Statkus/motion_platform/hardware/seat_mover/sway_motor_mount_top.FCStd

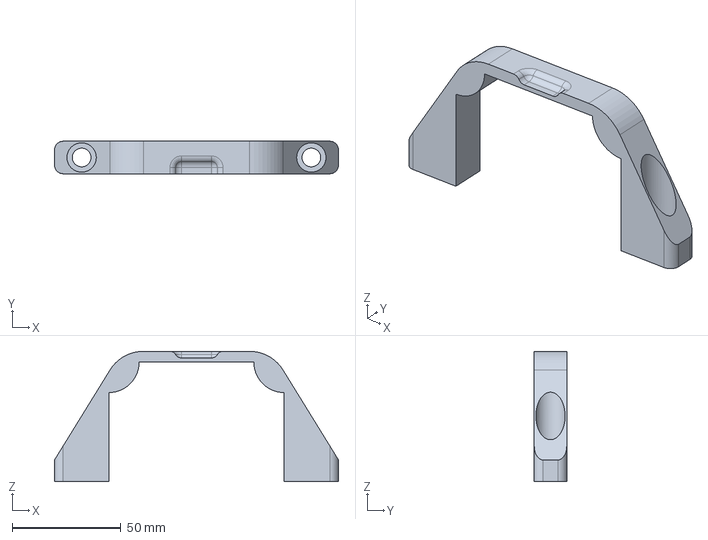
[picture p13: CAD file, 2025-09-17]
hardware/seat_mover/sway_motor_mount_top.FCStd
130.8 x 15.0 x 60.0 mm
