Statkus/motion_platform/hardware/parts_library/zip_tie_2x1_mm_to_2020_profile.FCStd

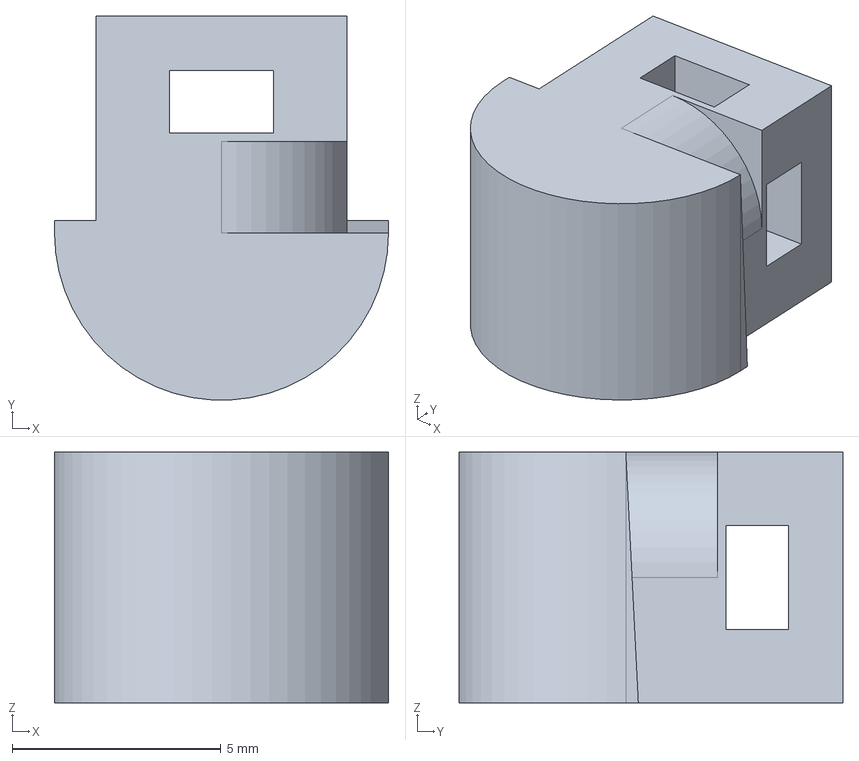
[picture p14: CAD file, 2025-10-09]
hardware/parts_library/zip_tie_2x1_mm_to_2020_profile.FCStd
8.00 x 9.19 x 6.00 mm
