Statkus/motion_platform/hardware/seat_mover/seat.FCStd

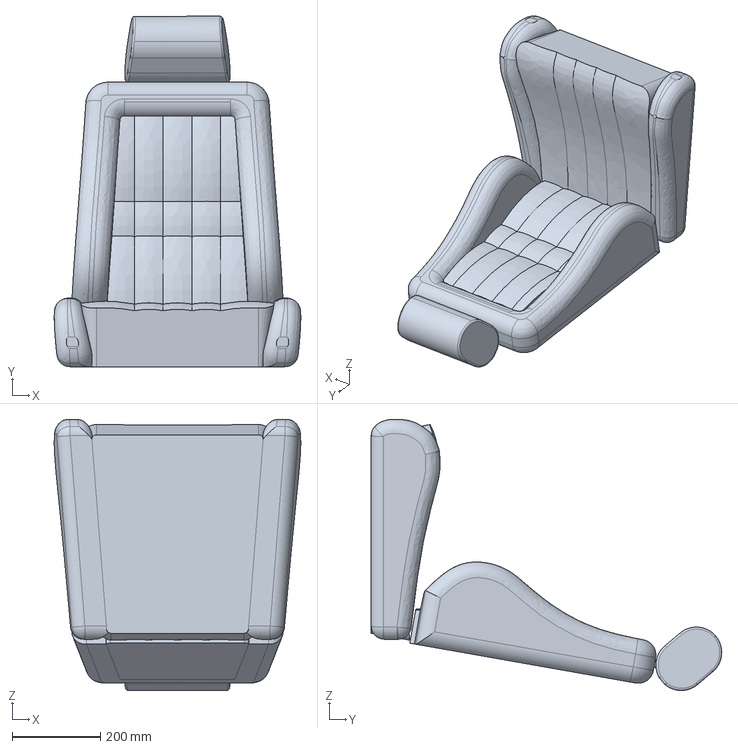
[picture p15: CAD file, 2025-09-17]
hardware/seat_mover/seat.FCStd
559.4 x 795.1 x 614.7 mm
