Statkus/motion_platform/hardware/parts_library/SHF25.FCStd

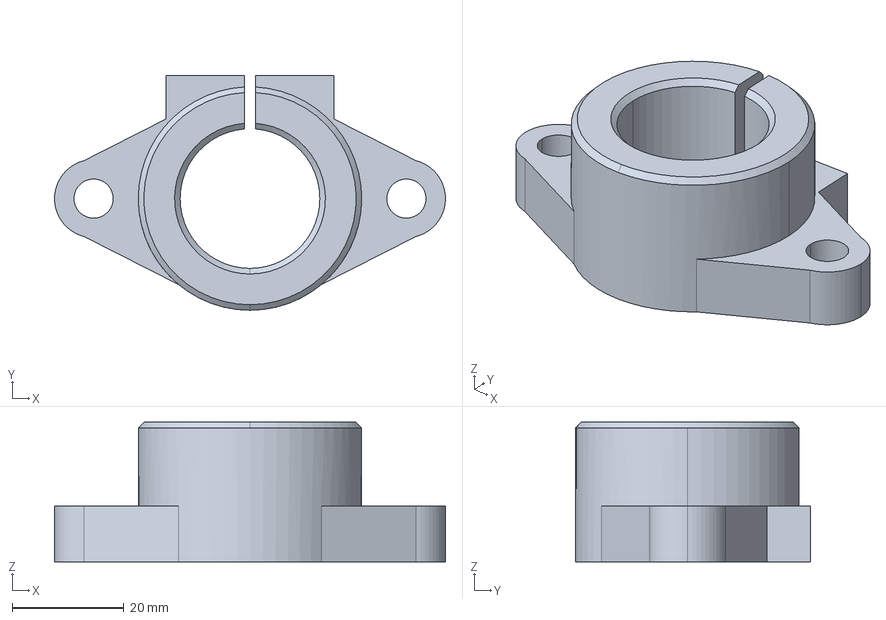
[picture p16: CAD file, 2025-08-28]
hardware/parts_library/SHF25.FCStd
70.0 x 42.0 x 25.0 mm
