Statkus/motion_platform/hardware/seat_mover/sway_motor_mount_bottom.FCStd

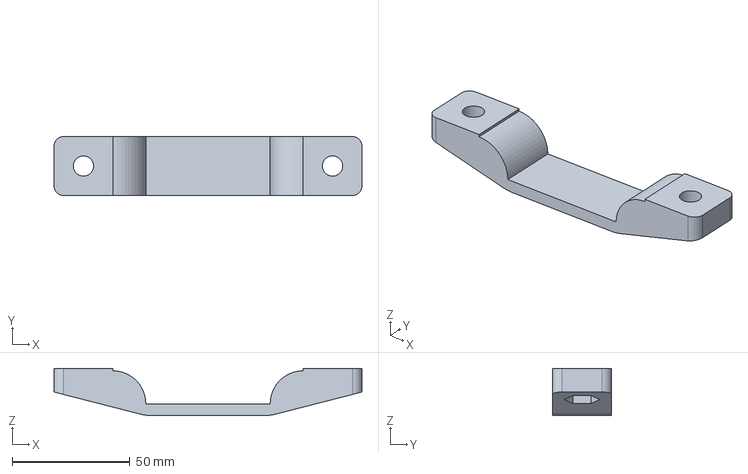
[picture p17: CAD file, 2025-09-17]
hardware/seat_mover/sway_motor_mount_bottom.FCStd
130.8 x 25.0 x 20.0 mm
