Statkus/motion_platform/hardware/parts_library/DSG16H_to_SH25.FCStd

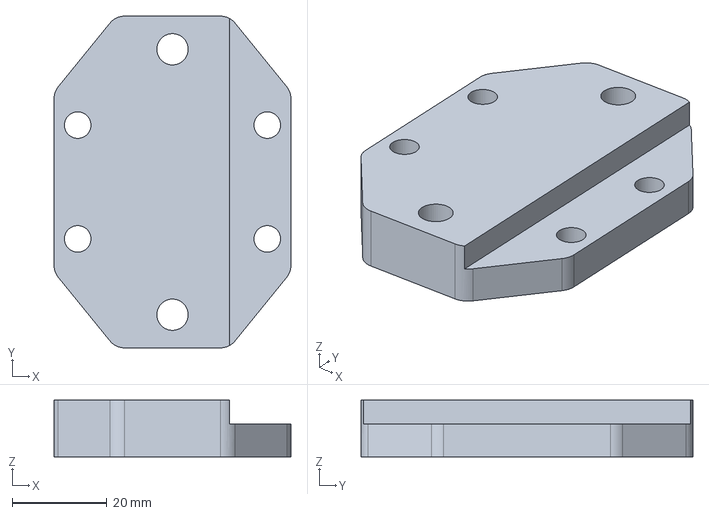
[picture p18: CAD file, 2025-08-28]
hardware/parts_library/DSG16H_to_SH25.FCStd
50.0 x 70.0 x 12.0 mm
