Statkus/motion_platform/hardware/parts_library/SFU1605.FCStd

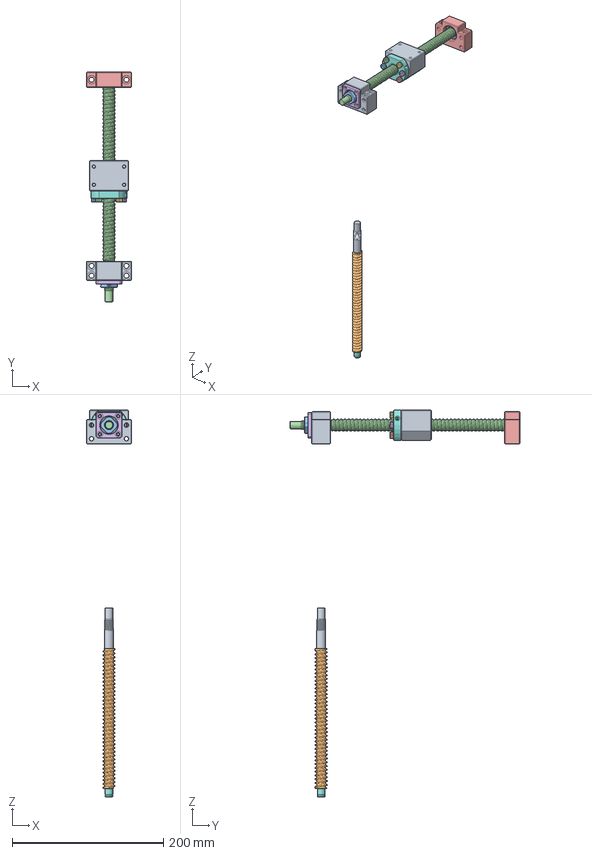
[picture p19: CAD file, 2025-08-28]
hardware/parts_library/SFU1605.FCStd
60.0 x 303.5 x 511.5 mm
BK12 v3
BK12 v004
BK12 v005
BK12 v006
BK12 v007
BK12 v008
BK12 v009
BK12 v010
BK12 v011
BK12 v012
BK12 v013
BK12 v014
BK12 v015
BK12 v016
BK12 v017
BK12 v018
BK12 v019
BK12 v020
BK12 v021
BK12 v022
BK12 v023
BK12 v024
BK12 v025
BK12 v026
BK12 v027
BK12 v028
BK12 v029
BK12 v030
BK12 v031
BK12 v032
BK12 v033
BK12 v034
BK12 v035
BK12 v036
BK12 v037
SFU1605_ball_screw_300mm
BF12 v4
BF12 v005
BF12 v006
BF12 v007
BF12 v008
BF12 v009
BF12 v010
BF12 v011
BF12 v012
BF12 v013
BF12 v014
SFU1605_ball_screw_nut
DSG16H
screw_DIN912_M5x20_000
screw_DIN912_M5x20_001
screw_DIN912_M5x20_002
screw_DIN912_M5x20_003
screw_DIN912_M5x20_004
screw_DIN912_M5x20_005
