Statkus/motion_platform/hardware/seat_mover/sway_motor_mount_side.FCStd

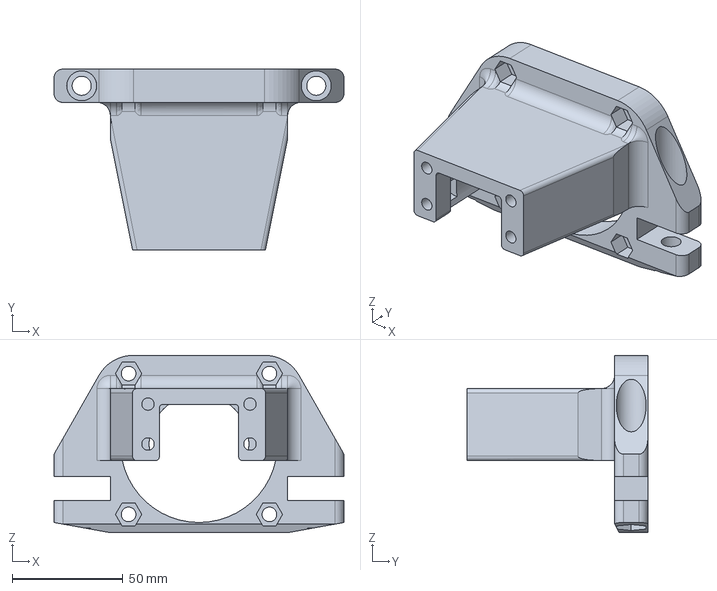
[picture p20: CAD file, 2025-09-17]
hardware/seat_mover/sway_motor_mount_side.FCStd
130.8 x 81.5 x 80.0 mm
