Statkus/motion_platform/hardware/parts_library/SC25UU_to_SH25.FCStd

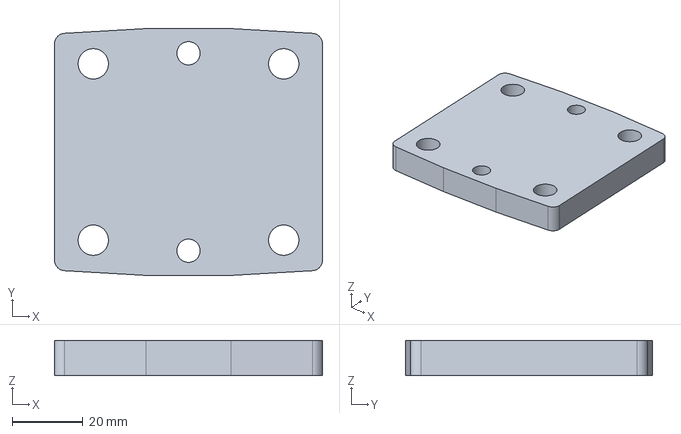
[picture p21: CAD file, 2025-08-28]
hardware/parts_library/SC25UU_to_SH25.FCStd
76.0 x 70.0 x 10.0 mm
