Statkus/motion_platform/hardware/seat_mover/sway_motor_mount_front_plate_shaft_support.FCStd

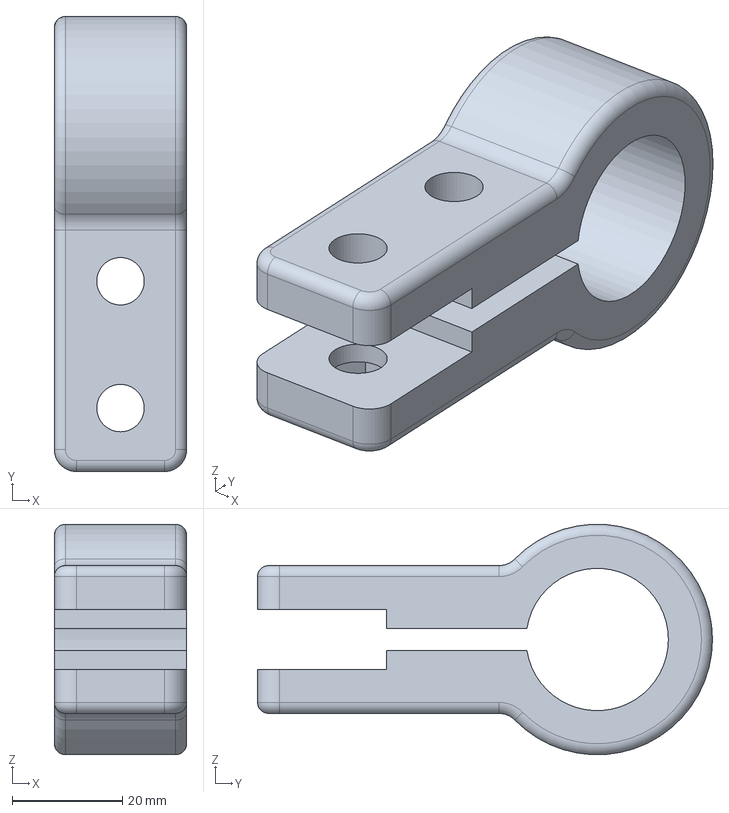
[picture p22: CAD file, 2025-09-17]
hardware/seat_mover/sway_motor_mount_front_plate_shaft_support.FCStd
24.0 x 82.5 x 41.7 mm
