Statkus/motion_platform/hardware/parts_library/profile_40_serie.FCStd

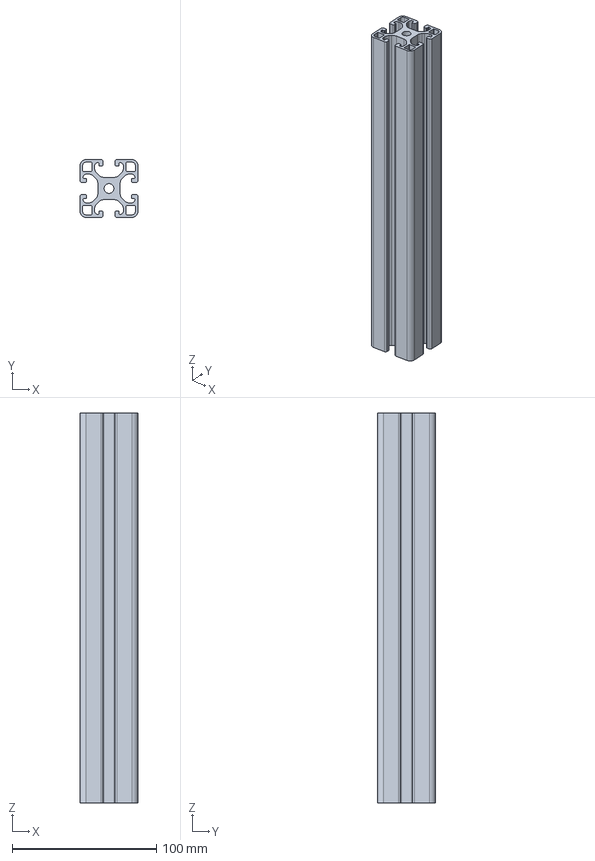
[picture p23: CAD file, 2025-08-28]
hardware/parts_library/profile_40_serie.FCStd
40.0 x 40.0 x 270.0 mm
