Statkus/motion_platform/hardware/parts_library/coupler.FCStd

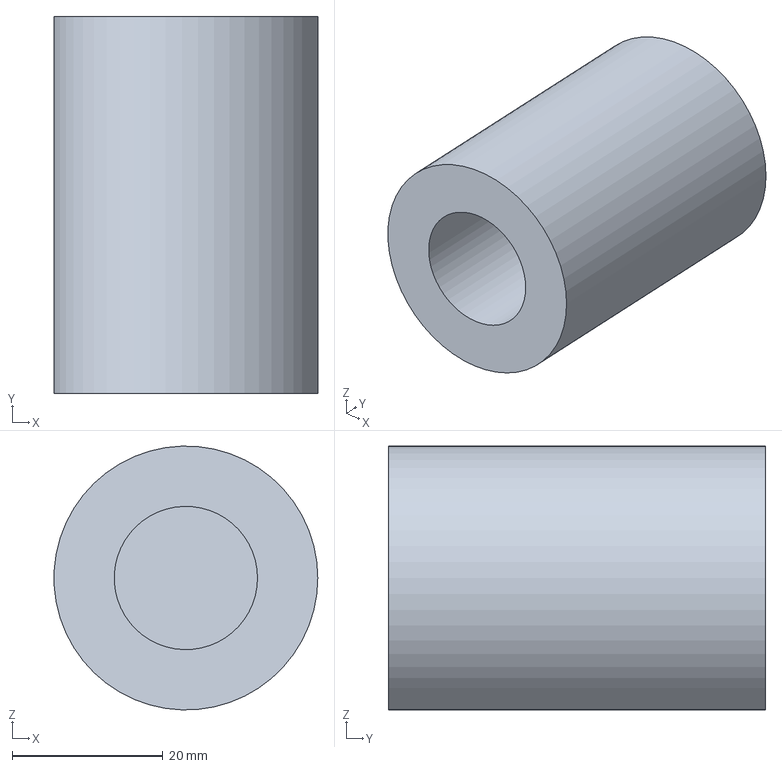
[picture p24: CAD file, 2025-08-28]
hardware/parts_library/coupler.FCStd
35.0 x 50.0 x 35.0 mm
