Statkus/motion_platform/hardware/seat_mover/surge_motor_mount_bottom.FCStd

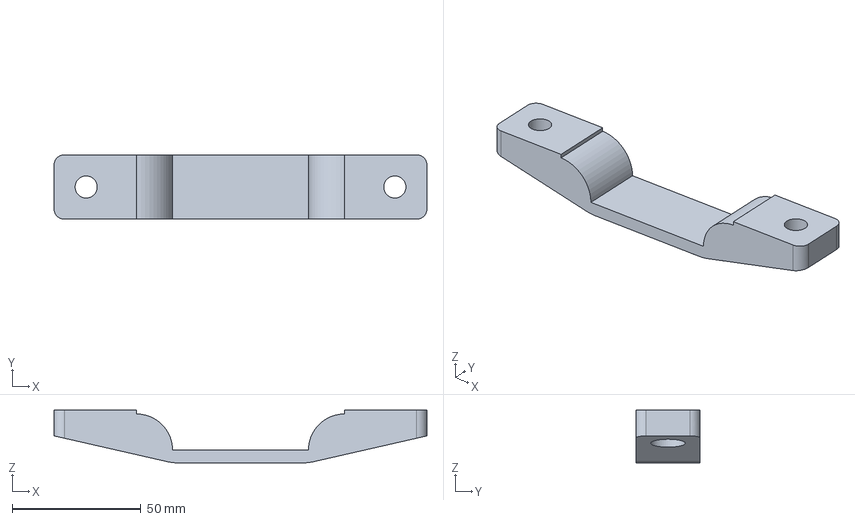
[picture p25: CAD file, 2025-09-17]
hardware/seat_mover/surge_motor_mount_bottom.FCStd
145.0 x 25.0 x 20.5 mm
