Statkus/motion_platform/hardware/parts_library/DSG16H_to_profile_40x40.FCStd

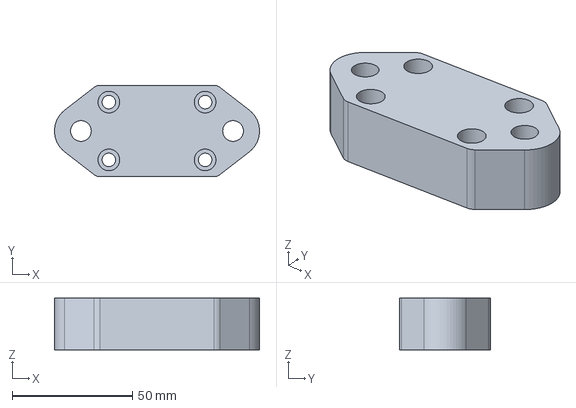
[picture p26: CAD file, 2025-08-28]
hardware/parts_library/DSG16H_to_profile_40x40.FCStd
85.2 x 38.0 x 21.5 mm
