Statkus/motion_platform/hardware/parts_library/linear_shaft.FCStd

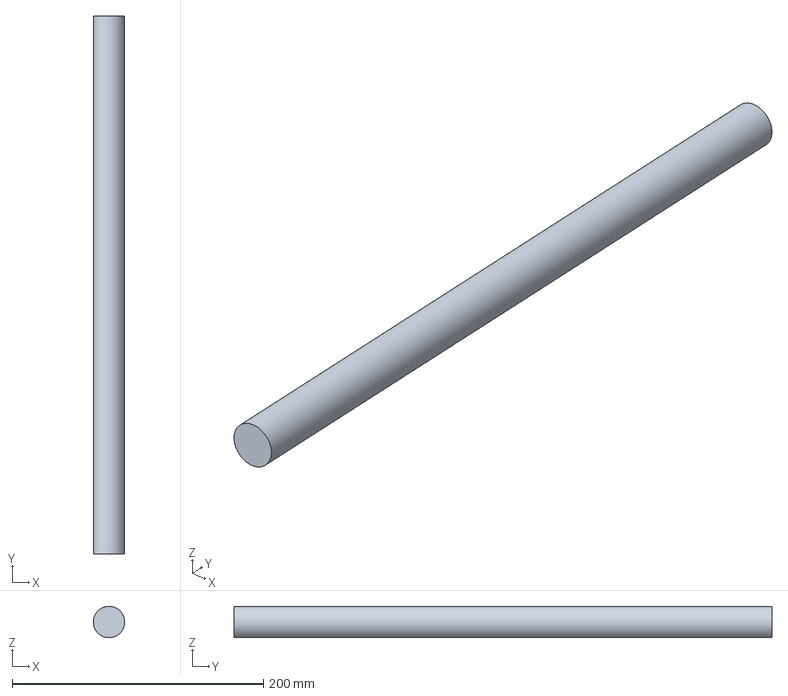
[picture p27: CAD file, 2025-08-28]
hardware/parts_library/linear_shaft.FCStd
25.0 x 428.0 x 25.0 mm
