Statkus/motion_platform/hardware/seat_mover/surge_BK12_mount_bottom.FCStd

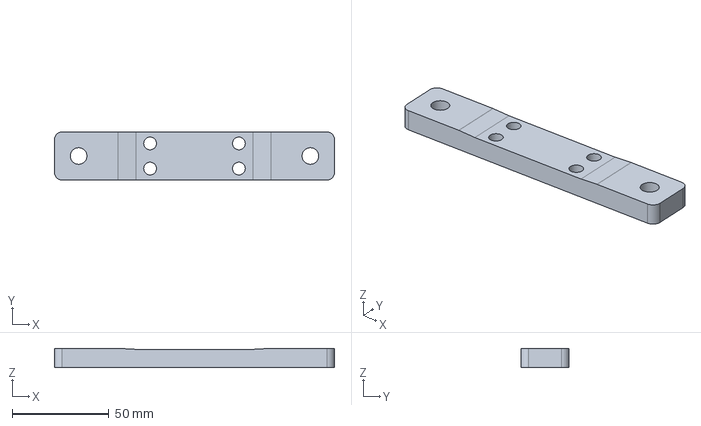
[picture p28: CAD file, 2025-09-17]
hardware/seat_mover/surge_BK12_mount_bottom.FCStd
145.0 x 25.0 x 10.0 mm
