Statkus/motion_platform/hardware/parts_library/motor.FCStd

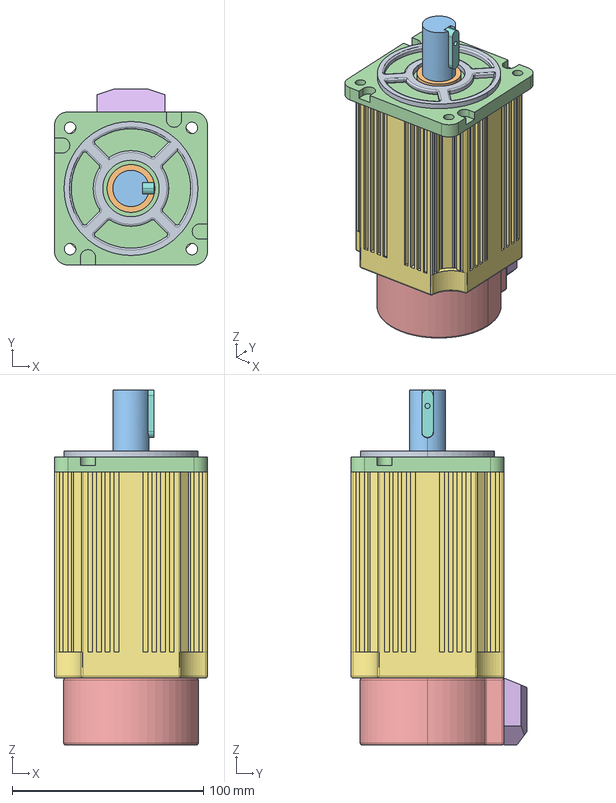
[picture p29: CAD file, 2025-08-28]
hardware/parts_library/motor.FCStd
80.0 x 92.0 x 185.6 mm
SERVOMOTOR 80ST-M02430
SERVOMOTOR 80ST-M02431
SERVOMOTOR 80ST-M02432
SERVOMOTOR 80ST-M02433
SERVOMOTOR 80ST-M02434
SERVOMOTOR 80ST-M02435
SERVOMOTOR 80ST-M02436
SERVOMOTOR 80ST-M02437
