Statkus/motion_platform/hardware/seat_mover/surge_BK12_mount_top.FCStd

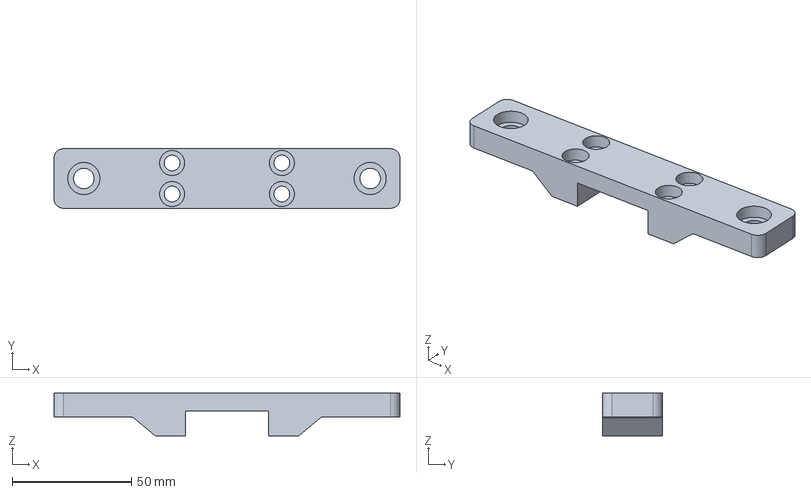
[picture p30: CAD file, 2025-09-17]
hardware/seat_mover/surge_BK12_mount_top.FCStd
145.0 x 25.0 x 18.0 mm
