Statkus/motion_platform/hardware/stl_files_to_print/surge_motor_mount_top.stl

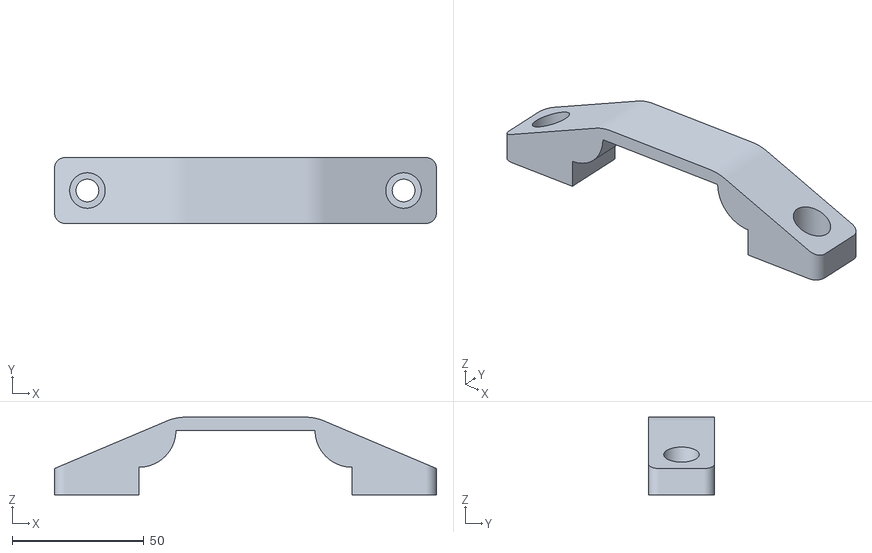
[picture p31: CAD file, 2025-09-17]
hardware/stl_files_to_print/surge_motor_mount_top.stl
145.0 x 25.0 x 29.5
