Statkus/motion_platform/hardware/parts_library/SC25UU.FCStd

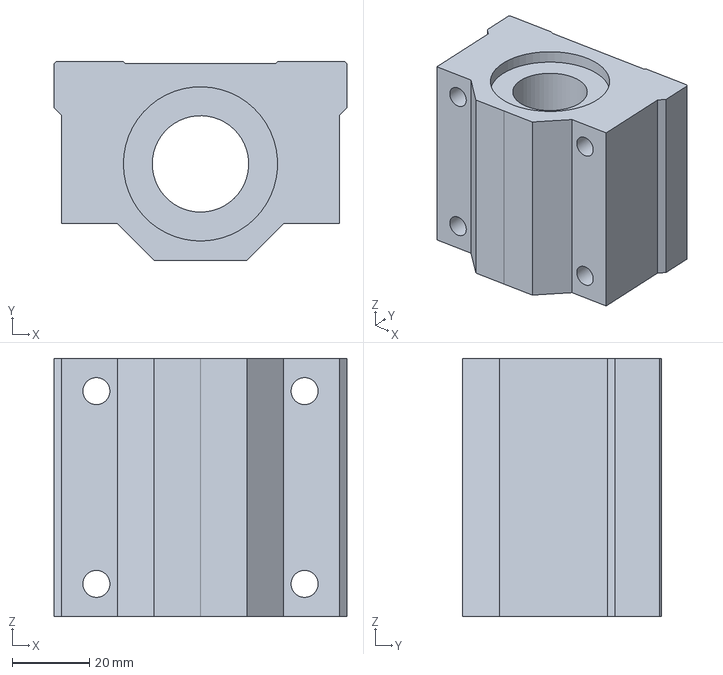
[picture p32: CAD file, 2025-08-28]
hardware/parts_library/SC25UU.FCStd
76.0 x 51.5 x 67.0 mm
