Statkus/motion_platform/hardware/seat_mover/surge_BK12_support.FCStd

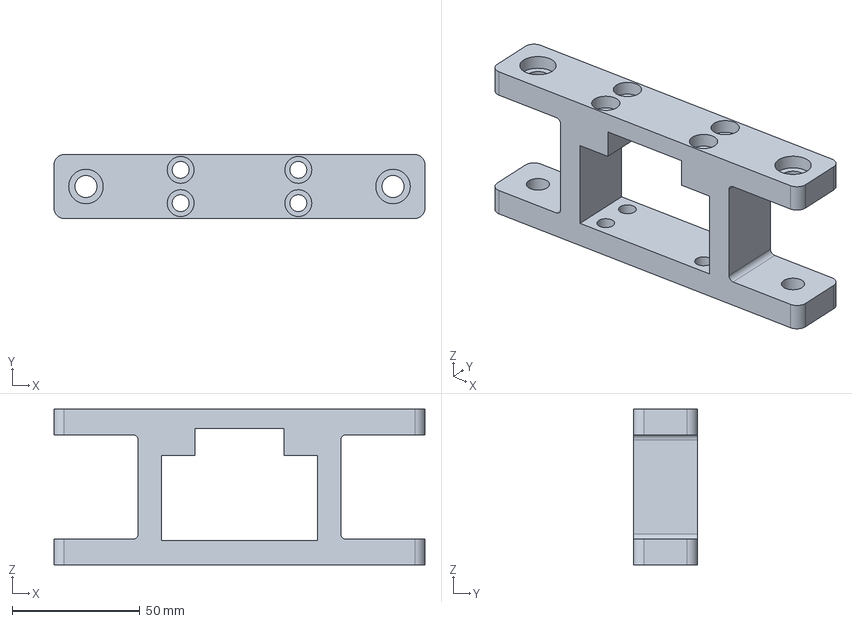
[picture p33: CAD file, 2025-09-17]
hardware/seat_mover/surge_BK12_support.FCStd
145.0 x 25.0 x 60.8 mm
