Statkus/motion_platform/hardware/parts_library/corner_bracket_40x40.FCStd

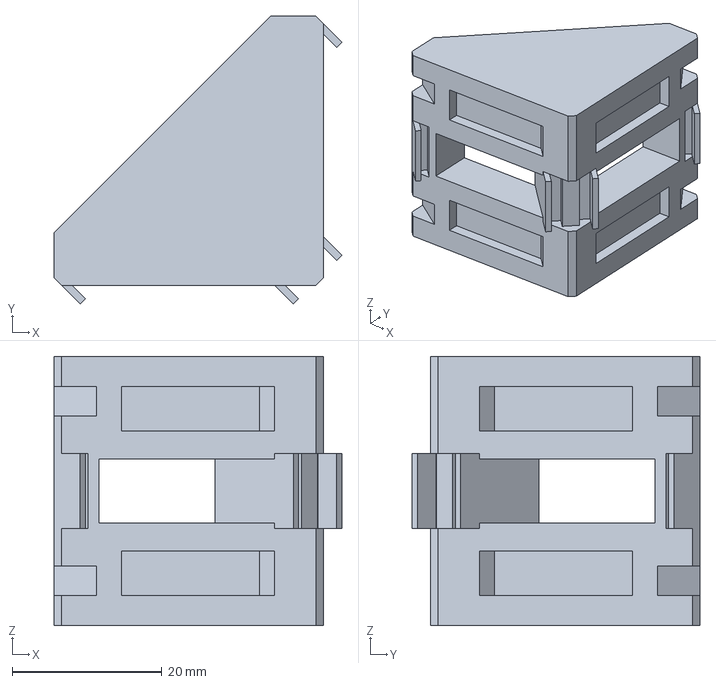
[picture p34: CAD file, 2025-08-28]
hardware/parts_library/corner_bracket_40x40.FCStd
38.5 x 38.5 x 36.0 mm
