Statkus/motion_platform/hardware/seat_mover/surge_motor_mount_top.FCStd

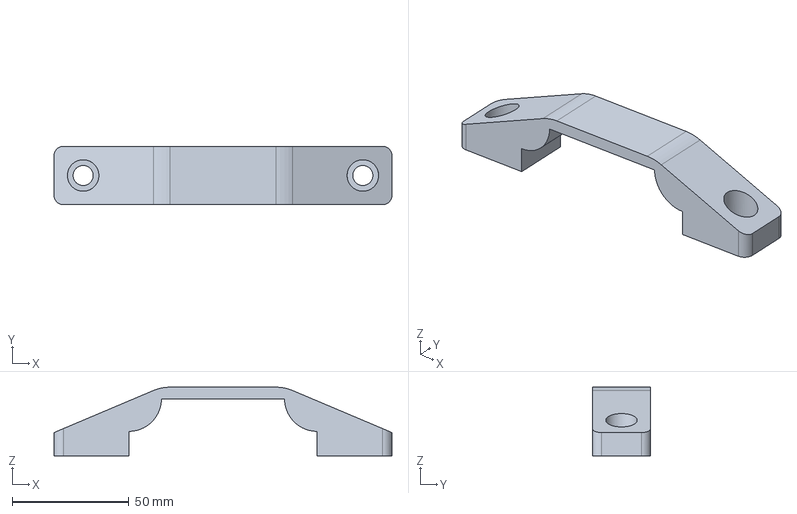
[picture p35: CAD file, 2025-09-17]
hardware/seat_mover/surge_motor_mount_top.FCStd
145.0 x 25.0 x 29.5 mm
