Statkus/motion_platform/hardware/parts_library/SH25.FCStd

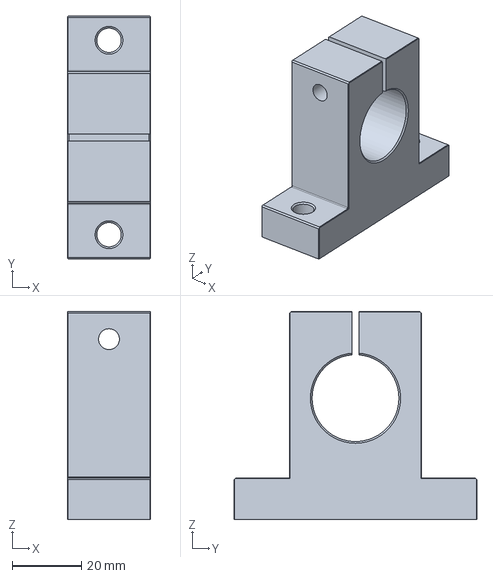
[picture p36: CAD file, 2025-08-28]
hardware/parts_library/SH25.FCStd
24.0 x 70.0 x 60.0 mm
