Statkus/motion_platform/hardware/seat_mover/surge_motor_mount_side.FCStd

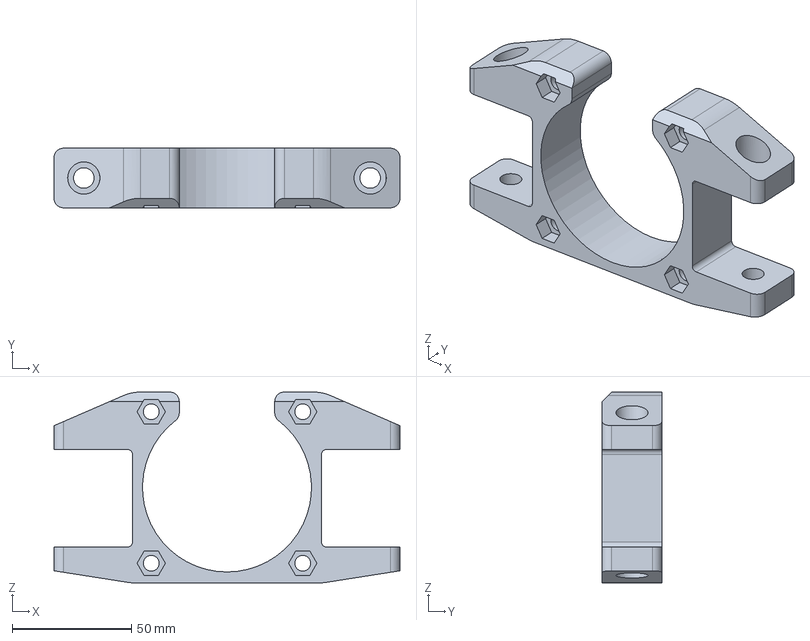
[picture p37: CAD file, 2025-09-17]
hardware/seat_mover/surge_motor_mount_side.FCStd
145.0 x 25.0 x 80.0 mm
