Statkus/motion_platform/hardware/stl_files_to_print/surge_motor_mount_side.stl

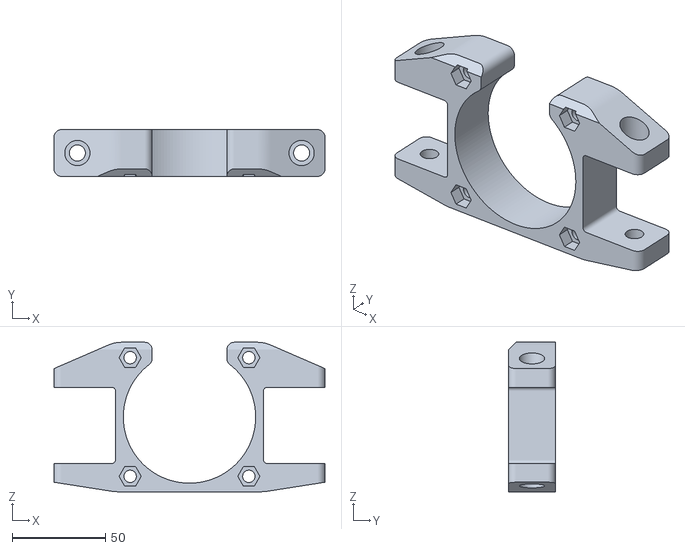
[picture p38: CAD file, 2025-09-17]
hardware/stl_files_to_print/surge_motor_mount_side.stl
145.0 x 25.0 x 80.0
