Statkus/motion_platform/hardware/stl_files_to_print/sway_motor_mount_front_plate_shaft_support.stl

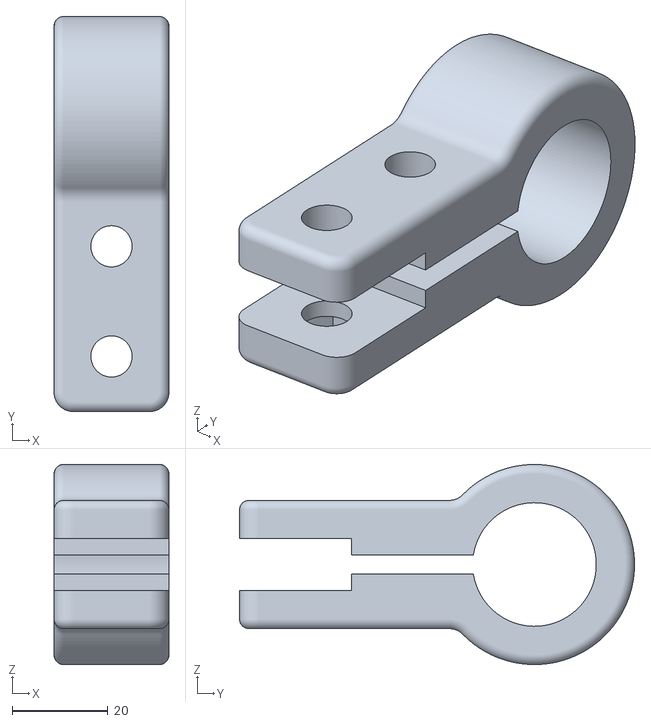
[picture p39: CAD file, 2025-09-17]
hardware/stl_files_to_print/sway_motor_mount_front_plate_shaft_support.stl
24.0 x 82.5 x 41.8
